AbraLoyMa/LG_OLED_Screensaver/RadarControl.h

enum Bluetooth: int {
  ENABLE = 1,
  DISABLE = 2
};

enum Mode: int {
  SETUP = 0,
  RESTART = 3
};

const PROGMEM byte command[][14] = {    //Store the commands in ROM
  {0xFD, 0xFC, 0xFB, 0xFA, 0x04, 0x00, 0xFF, 0x00, 0x01, 0x00, 0x04, 0x03, 0x02, 0x01},
  {0xFD, 0xFC, 0xFB, 0xFA, 0x04, 0x00, 0xA4, 0x00, 0x01, 0x00, 0x04, 0x03, 0x02, 0x01},
  {0xFD, 0xFC, 0xFB, 0xFA, 0x04, 0x00, 0xA4, 0x00, 0x00, 0x00, 0x04, 0x03, 0x02, 0x01},
  {0xFD, 0xFC, 0xFB, 0xFA, 0x02, 0x00, 0xA3, 0x00, 0x04, 0x03, 0x02, 0x01},
};
